ADElectronics/1986BE4-Dev-Board/Firmware/MDR1986BE4_StdPeriph_Driver/src/MDR32F9Qx_dma.c

/**
  * FILE MDR32F9Qx_dma.c
  */

/* Includes ------------------------------------------------------------------*/
#include "MDR32F9Qx_config.h"
#include "MDR32F9Qx_dma.h"

#define ASSERT_INFO_FILE_ID FILEID__MDR32F9X_DMA_C

/** @addtogroup __MDR32F9Qx_StdPeriph_Driver MDR32F9Qx Standard Peripherial Driver
  * @{
  */

/** @defgroup DMA DMA
  * @{
  */

/** @defgroup DMA_Private_Constants DMA Private Constants
  * @{
  */

#define DMA_CONTROL_MINUS_1   ((uint32_t)0x3FF0)      /* DMA control "n_minus_1" field mask */

/** @} */ /* End of group DMA_Private_Constants */

/** @defgroup DMA_Private_Variables DMA Private Variables
  * @{
  */

/**
  * @brief  DMA Channel Control Data Table
  */

/* Select data alignment */
#if (DMA_Channels_Number == 1)
#define DATA_ALIGN 32
#elif (DMA_Channels_Number == 2)
#define DATA_ALIGN 64
#elif ((DMA_Channels_Number >= 3) && (DMA_Channels_Number <= 4))
#define DATA_ALIGN 128
#elif ((DMA_Channels_Number >= 5) && (DMA_Channels_Number <= 8))
#define DATA_ALIGN 256
#elif ((DMA_Channels_Number >= 9) && (DMA_Channels_Number <= 16))
#define DATA_ALIGN 512
#elif ((DMA_Channels_Number >= 17) && (DMA_Channels_Number <= 32))
#define DATA_ALIGN 1024
#endif

#if defined ( __ICCARM__ )
  #pragma data_alignment = DATA_ALIGN
	DMA_CtrlDataTypeDef DMA_ControlTable[DMA_Channels_Number * (1 + DMA_AlternateData)];
#endif

#if defined ( __CMCARM__ )
	#pragma locate DMA_ControlTable 0x20000000 noinit
	DMA_CtrlDataTypeDef DMA_ControlTable[DMA_Channels_Number * (1 + DMA_AlternateData)];
#elif defined ( __CC_ARM )
	DMA_CtrlDataTypeDef DMA_ControlTable[DMA_Channels_Number * (1 + DMA_AlternateData)] __attribute__ ((aligned (DATA_ALIGN)));
#elif defined ( __GNUC__ )
	DMA_CtrlDataTypeDef DMA_ControlTable[DMA_Channels_Number * (1 + DMA_AlternateData)] __attribute__((aligned(DATA_ALIGN)));
#endif


/** @} */ /* End of group DMA_Private_Variables */

/** @defgroup DMA_Private_FunctionPrototypes DMA Private Function Prototypes
  * @{
  */

void DMA_CtrlDataInit(DMA_CtrlDataInitTypeDef *DMA_ctrl_data_ptr, DMA_CtrlDataTypeDef *DMA_ctrl_table_ptr);

/** @} */ /* End of group DMA_Private_FunctionPrototypes */

/** @defgroup DMA_Private_Functions DMA Private Functions
  * @{
  */

/**
  * @brief  Initializes the DMA control data structure according to the specified
  *         parameters.
  * @param  DMA_ctrl_data_ptr: pointer to a DMA_CtrlDataInitTypeDef structure that
  *         contains the control data structure to initialize
  * @param  DMA_ctrl_table_ptr: pointer to a DMA_CtrlDataTypeDef structure that
  *         contains the initial control data configuration, provided by the application.
  * @retval None
  */
void DMA_CtrlDataInit(DMA_CtrlDataInitTypeDef *DMA_ctrl_data_ptr, DMA_CtrlDataTypeDef *DMA_ctrl_table_ptr)
{
  /* Check DMA configuration parameters */
  assert_param(IS_DMA_CHANNELS(DMA_Channels_Number));
  assert_param(IS_DMA_ALTERNATE_DATA(DMA_AlternateData));

  /* Check the parameters */
  assert_param(IS_DMA_SOURCE_INC_STATE(DMA_ctrl_data_ptr->DMA_SourceIncSize));
  assert_param(IS_DMA_DEST_INC_STATE(DMA_ctrl_data_ptr->DMA_DestIncSize));
  assert_param(IS_DMA_MEMORY_DATA_SIZE(DMA_ctrl_data_ptr->DMA_MemoryDataSize));
  assert_param(IS_DMA_MODE(DMA_ctrl_data_ptr->DMA_Mode));
  assert_param(IS_DMA_CYCLE_SIZE(DMA_ctrl_data_ptr->DMA_CycleSize));
  assert_param(IS_DMA_CONTINUOUS_NUMBER(DMA_ctrl_data_ptr->DMA_NumContinuous));
  assert_param(IS_DMA_SOURCE_PROT(DMA_ctrl_data_ptr->DMA_SourceProtCtrl));
  assert_param(IS_DMA_DEST_PROT(DMA_ctrl_data_ptr->DMA_DestProtCtrl));

  /* DMA Source Data End Address */
  if (DMA_ctrl_data_ptr->DMA_SourceIncSize == DMA_SourceIncNo)
  {
    DMA_ctrl_table_ptr->DMA_SourceEndAddr = DMA_ctrl_data_ptr->DMA_SourceBaseAddr;
  }
  else
  {
    DMA_ctrl_table_ptr->DMA_SourceEndAddr = ( DMA_ctrl_data_ptr->DMA_SourceBaseAddr +
        ((DMA_ctrl_data_ptr->DMA_CycleSize - 1) << (DMA_ctrl_data_ptr->DMA_SourceIncSize >> 26)));
  }

  /* DMA Destination Data End Address */
  if (DMA_ctrl_data_ptr->DMA_Mode == DMA_Mode_MemScatterPri)
  {
    /* Memory Scatter-Gather mode */
    DMA_ctrl_table_ptr->DMA_DestEndAddr = (DMA_ctrl_data_ptr->DMA_DestBaseAddr + 12);
  }
  else
  {
    /* Other modes */
    if (DMA_ctrl_data_ptr->DMA_DestIncSize == DMA_DestIncNo)
    {
      DMA_ctrl_table_ptr->DMA_DestEndAddr = DMA_ctrl_data_ptr->DMA_DestBaseAddr;
    }
    else
    {
      DMA_ctrl_table_ptr->DMA_DestEndAddr = ( DMA_ctrl_data_ptr->DMA_DestBaseAddr +
        ((DMA_ctrl_data_ptr->DMA_CycleSize - 1) << (DMA_ctrl_data_ptr->DMA_DestIncSize >> 30)));
    }
  }

  /* DMA Control Data */
  DMA_ctrl_table_ptr->DMA_Control = (DMA_ctrl_data_ptr->DMA_DestIncSize     |
                                     DMA_ctrl_data_ptr->DMA_MemoryDataSize  |
                                     DMA_ctrl_data_ptr->DMA_SourceIncSize   |
                                     DMA_ctrl_data_ptr->DMA_DestProtCtrl    |
                                     DMA_ctrl_data_ptr->DMA_SourceProtCtrl  |
                                     DMA_ctrl_data_ptr->DMA_NumContinuous   |
                                     ((DMA_ctrl_data_ptr->DMA_CycleSize - 1) << 4)  |
                                     DMA_ctrl_data_ptr->DMA_Mode);
}

/**
  * @brief  Deinitializes the DMA registers to their default reset values.
  * @param  None
  * @retval None
  */
void DMA_DeInit(void)
{
  MDR_DMA->CFG = 0;                           /* Master Enable Off */
  MDR_DMA->CTRL_BASE_PTR = 0;                 /* Control data base pointer */
  MDR_DMA->CHNL_SW_REQUEST = 0;               /* Disable all sw requests */
  MDR_DMA->CHNL_USEBURST_CLR = 0xFFFFFFFF;    /* Disable burst mode */
  MDR_DMA->CHNL_REQ_MASK_CLR = 0xFFFFFFFF;    /* Clear mask request */
  MDR_DMA->CHNL_ENABLE_CLR = 0xFFFFFFFF;      /* Clear channel enable */
  MDR_DMA->CHNL_PRI_ALT_CLR = 0xFFFFFFFF;     /* Reset to primary data structure */
  MDR_DMA->CHNL_PRIORITY_CLR = 0xFFFFFFFF;    /* Reset to default priority */
  MDR_DMA->ERR_CLR = 0x01;                    /* Clear dma_err status */
}

/**
  * @brief  Initializes the DMA Channel DMA_ControlTable structure according to the specified
  *         parameters.
  * @param  DMA_Channel: can be 0 to 31 or a value of @ref DMA_valid_channels to select the DMA Channel.
  * @param  DMA_CtrlDataType: can be DMA_CTRL_DATA_PRIMARY or DMA_CTRL_DATA_ALTERNATE
  * @param  DMA_CtrlStruct: pointer to a DMA_CtrlDataInitTypeDef structure that
  *         contains the initial control data configuration, provided by the application
  * 				for the specified DMA Channel.
  * @retval None
  */
void DMA_CtrlInit(uint8_t DMA_Channel, uint8_t DMA_CtrlDataType,  DMA_CtrlDataInitTypeDef* DMA_CtrlStruct)
{
  /* Primary Control Data Init */
  if (DMA_CtrlDataType == DMA_CTRL_DATA_PRIMARY)
  {
    DMA_CtrlDataInit(DMA_CtrlStruct, &DMA_ControlTable[DMA_Channel]);
  }
#if (DMA_AlternateData == 1)
  /* Alternate Control Data Init */
  else
  {
    uint32_t ptr = (MDR_DMA->ALT_CTRL_BASE_PTR + (DMA_Channel * sizeof(DMA_CtrlDataTypeDef)));
    DMA_CtrlDataInit(DMA_CtrlStruct, (DMA_CtrlDataTypeDef *)ptr);
  }
#endif
}

/**
  * @brief  Initializes the DMA Scatter-Gather Task structure according to the specified
  *         parameters.
  * @param  DMA_Task: specifies the current task number. Begins with 0.
  * @param  DMA_CtrlStruct: pointer to a DMA_CtrlDataInitTypeDef structure that
  *         contains the control data information for the specified task.
  * @param  DMA_SG_TaskArray: pointer to a DMA_CtrlDataTypeDef array that
  *         contains the copy of the alternate control data information for the specified task.
  * @retval None
  */
void DMA_SG_CtrlInit(uint32_t DMA_Task, DMA_CtrlDataTypeDef *DMA_SG_TaskArray,  DMA_CtrlDataInitTypeDef* DMA_CtrlStruct)
{
  DMA_CtrlDataInit(DMA_CtrlStruct, &DMA_SG_TaskArray[DMA_Task]);
}

/**
  * @brief  Initializes the DMA Channel in Memory Scatter-Gather mode
  * @param  DMA_Channel: can be 0 to 31 or a value of @ref DMA_valid_channels to select the DMA Channel.
  * @param  DMA_SG_InitStruct: pointer to a DMA_Channel_SG_InitTypeDef array that
  *         contains the configuration information for the specified DMA Channel.
  * @retval None
  */
void DMA_SG_Init( uint8_t DMA_Channel, DMA_Channel_SG_InitTypeDef *DMA_SG_InitStruct)
{
  DMA_CtrlDataInitTypeDef DMA_PriCtrlData;

  /* Check the parameters */
  assert_param(DMA_AlternateData == 1);
  assert_param(DMA_SG_InitStruct != 0);
  assert_param(DMA_SG_InitStruct->DMA_SG_TaskNumber != 0);
  assert_param(IS_DMA_CHANNEL(DMA_Channel));
  assert_param(IS_DMA_AHB_PROT(DMA_SG_InitStruct->DMA_ProtCtrl));
  assert_param(IS_DMA_PRIORITY(DMA_SG_InitStruct->DMA_Priority));
  assert_param(IS_DMA_SOURCE_PROT(DMA_SG_InitStruct->DMA_SourceProtCtrl));
  assert_param(IS_DMA_DEST_PROT(DMA_SG_InitStruct->DMA_DestProtCtrl));
  assert_param(IS_DMA_BURST(DMA_SG_InitStruct->DMA_UseBurst));

  /* Check the CTRL_BASE_PTR initialisation */
  MDR_DMA->CTRL_BASE_PTR = (uint32_t)DMA_ControlTable;

  /* Primary Control Data Init */
  DMA_PriCtrlData.DMA_SourceBaseAddr = (uint32_t)(DMA_SG_InitStruct->DMA_SG_TaskArray);
  DMA_PriCtrlData.DMA_DestBaseAddr = (MDR_DMA->ALT_CTRL_BASE_PTR + (DMA_Channel * sizeof(DMA_CtrlDataTypeDef)));
  DMA_PriCtrlData.DMA_SourceIncSize = DMA_SourceIncWord;
  DMA_PriCtrlData.DMA_DestIncSize = DMA_DestIncWord;
  DMA_PriCtrlData.DMA_MemoryDataSize = DMA_MemoryDataSize_Word;
  DMA_PriCtrlData.DMA_Mode = DMA_Mode_MemScatterPri;
  DMA_PriCtrlData.DMA_CycleSize = DMA_SG_InitStruct->DMA_SG_TaskNumber << 2;
  DMA_PriCtrlData.DMA_NumContinuous = DMA_Transfers_4;
  DMA_PriCtrlData.DMA_SourceProtCtrl = DMA_SG_InitStruct->DMA_SourceProtCtrl;
  DMA_PriCtrlData.DMA_DestProtCtrl = DMA_SG_InitStruct->DMA_DestProtCtrl;

  DMA_CtrlDataInit(&DMA_PriCtrlData, &DMA_ControlTable[DMA_Channel]);

  /* DMA configuration register */
  MDR_DMA->CFG = DMA_CFG_MASTER_ENABLE | DMA_SG_InitStruct->DMA_ProtCtrl;

  /* Burst mode */
  if (DMA_SG_InitStruct->DMA_UseBurst == DMA_BurstSet)
  {
    MDR_DMA->CHNL_USEBURST_SET = (1 << DMA_Channel);
  }
  else
  {
    MDR_DMA->CHNL_USEBURST_CLR = (1 << DMA_Channel);
  }

  /* Channel mask clear */
  MDR_DMA->CHNL_REQ_MASK_CLR = (1 << DMA_Channel);

  /* Enable channel */
  MDR_DMA->CHNL_ENABLE_SET = (1 << DMA_Channel);

  /* Primary - Alternate control data structure selection */
  MDR_DMA->CHNL_PRI_ALT_CLR = (1 << DMA_Channel);       /* Use Primary */

  /* Channel priority set */
  if (DMA_SG_InitStruct->DMA_Priority == DMA_Priority_High)
  {
    MDR_DMA->CHNL_PRIORITY_SET = (1 << DMA_Channel);      /* High priority */
  }
  else
  {
    MDR_DMA->CHNL_PRIORITY_CLR = (1 << DMA_Channel);      /* Default priority */
  }
}

/**
  * @brief  Initializes the DMA Channel according to the specified
  *         parameters in the DMA_InitStruct.
  * @param  DMA_Channel: can be 0 to 31 or a value of @ref DMA_valid_channels to select the DMA Channel.
  * @param  DMA_InitStruct: pointer to a DMA_ChannelInitTypeDef structure that
  *         contains the configuration information for the specified DMA Channel.
  * @retval None
  */
void DMA_Init(uint8_t DMA_Channel, DMA_ChannelInitTypeDef* DMA_InitStruct)
{
  /* Check the parameters */
  assert_param(IS_DMA_CHANNEL(DMA_Channel));
  assert_param(IS_DMA_AHB_PROT(DMA_InitStruct->DMA_ProtCtrl));
  assert_param(IS_DMA_PRIORITY(DMA_InitStruct->DMA_Priority));
  assert_param(IS_DMA_BURST(DMA_InitStruct->DMA_UseBurst));
  assert_param(IS_DMA_SELECT_DATA_STRUCTURE(DMA_InitStruct->DMA_SelectDataStructure));

  /* Check the CTRL_BASE_PTR initialisation */
  MDR_DMA->CTRL_BASE_PTR = (uint32_t)DMA_ControlTable;

  /* Primary Control Data Init */
  if (DMA_InitStruct->DMA_PriCtrlData)
  {
    DMA_CtrlDataInit(DMA_InitStruct->DMA_PriCtrlData, &DMA_ControlTable[DMA_Channel]);
  }

#if (DMA_AlternateData == 1)
  /* Alternate Control Data Init */
  if (DMA_InitStruct->DMA_AltCtrlData)
  {
    uint32_t ptr = (MDR_DMA->ALT_CTRL_BASE_PTR + (DMA_Channel * sizeof(DMA_CtrlDataTypeDef)));
    DMA_CtrlDataInit(DMA_InitStruct->DMA_AltCtrlData, (DMA_CtrlDataTypeDef *)ptr);
  }
#endif

  /* DMA configuration register */
  MDR_DMA->CFG = DMA_CFG_MASTER_ENABLE | DMA_InitStruct->DMA_ProtCtrl;

  /* Burst mode */
  if (DMA_InitStruct->DMA_UseBurst == DMA_BurstSet)
  {
    MDR_DMA->CHNL_USEBURST_SET = (1 << DMA_Channel);
  }
  else
  {
    MDR_DMA->CHNL_USEBURST_CLR = (1 << DMA_Channel);
  }

  /* Channel mask clear */
  MDR_DMA->CHNL_REQ_MASK_CLR = (1 << DMA_Channel);

  /* Enable channel */
  MDR_DMA->CHNL_ENABLE_SET = (1 << DMA_Channel);

  /* Primary - Alternate control data structure selection */
  if (DMA_InitStruct->DMA_SelectDataStructure == DMA_CTRL_DATA_PRIMARY)
  {
    MDR_DMA->CHNL_PRI_ALT_CLR = (1 << DMA_Channel);       /* Use Primary */
  }
  else
  {
    MDR_DMA->CHNL_PRI_ALT_SET = (1 << DMA_Channel);       /* Use Alternate */
  }

  /* Channel priority set */
  if (DMA_InitStruct->DMA_Priority == DMA_Priority_High)
  {
    MDR_DMA->CHNL_PRIORITY_SET = (1 << DMA_Channel);      /* High priority */
  }
  else
  {
    MDR_DMA->CHNL_PRIORITY_CLR = (1 << DMA_Channel);      /* Default priority */
  }
}

/**
  * @brief  Fills each DMA_InitStruct member with its default value.
  * @param  DMA_InitStruct : pointer to a DMA_ChannelInitTypeDef structure which will
  *         be initialized.
  * @retval None
  */
void DMA_StructInit(DMA_ChannelInitTypeDef* DMA_InitStruct)
{
  DMA_InitStruct->DMA_PriCtrlData = 0;
  DMA_InitStruct->DMA_AltCtrlData = 0;
  DMA_InitStruct->DMA_ProtCtrl = 0;
  DMA_InitStruct->DMA_Priority = 0;
  DMA_InitStruct->DMA_UseBurst = 0;
  DMA_InitStruct->DMA_SelectDataStructure = 0;
}

/**
  * @brief  Fills each DMA_SG_InitStruct member with its default value.
  * @param  DMA_SG_InitStruct : pointer to a DMA_Channel_SG_InitTypeDef structure which will
  *         be initialized.
  * @retval None
  */
void DMA_SG_StructInit(DMA_Channel_SG_InitTypeDef* DMA_SG_InitStruct)
{
  DMA_SG_InitStruct->DMA_SG_TaskArray = 0;
  DMA_SG_InitStruct->DMA_SG_TaskNumber = 0;
  DMA_SG_InitStruct->DMA_SourceProtCtrl = 0;
  DMA_SG_InitStruct->DMA_DestProtCtrl = 0;
  DMA_SG_InitStruct->DMA_ProtCtrl = 0;
  DMA_SG_InitStruct->DMA_Priority = 0;
  DMA_SG_InitStruct->DMA_UseBurst = 0;
}

/**
  * @brief  Enables or disables the specified DMA Channel.
  * @param  DMA_Channel: can be 0 to 31 or a value of @ref DMA_valid_channels to select the DMA Channel.
  * @param  NewState: new state of the DMA Channel.
  *         This parameter can be: ENABLE or DISABLE.
  * @retval None
  */
void DMA_Cmd(uint8_t DMA_Channel, FunctionalState NewState)
{
  /* Check the parameters */
  assert_param(IS_DMA_CHANNEL(DMA_Channel));

  /* Channel Enable/Disable */
  if ( NewState == ENABLE)
  {
    MDR_DMA->CHNL_ENABLE_SET = (1 << DMA_Channel);
  }
  else
  {
    MDR_DMA->CHNL_ENABLE_CLR = (1 << DMA_Channel);
  }
}

/**
  * @brief  Generates the specified DMA Channel software request.
  * @param  DMA_Channel: can be 0 to 31 or a value of @ref DMA_valid_channels to select the DMA Channel.
  * @retval None
  */
void DMA_Request(uint8_t DMA_Channel)
{
  /* Check the parameters */
  assert_param(IS_DMA_CHANNEL(DMA_Channel));

  /* Set SW Request */
  MDR_DMA->CHNL_SW_REQUEST = (1 << DMA_Channel);
}

/**
  * @brief  Clears the DMA Error bit.
  * @param  None
  * @retval None
  */
void DMA_ClearError(void)
{
  MDR_DMA->ERR_CLR = 0x01;            /* Clear dma_err status */
}

/**
  * @brief  Returns the number of remaining transfers in the current
  *         DMA Channel cycle.
  * @param  DMA_Channel: can be 0 to 31 or a value of @ref DMA_valid_channels to select the DMA Channel.
  * @param  DMA_CtrlData: specifies the primary / alternate control data table to check.
  *         This parameter can be a value of @ref DMA_data_structure_selection.
  * @retval The number of remaining transfers in the current DMA Channel
  *         cycle and the current control data structure.
  */
uint32_t DMA_GetCurrTransferCounter(uint8_t DMA_Channel, uint8_t DMA_CtrlData)
{
  DMA_CtrlDataTypeDef *ptr;     /* Pointer to the channels's data structure */

  /* Check the parameters */
  assert_param(IS_DMA_CHANNEL(DMA_Channel));
  assert_param(IS_DMA_SELECT_DATA_STRUCTURE(DMA_CtrlData));

  /* Init the control data pointer */
  if (DMA_CtrlData == DMA_CTRL_DATA_PRIMARY)
  {
    ptr = (DMA_CtrlDataTypeDef *)(MDR_DMA->CTRL_BASE_PTR + (DMA_Channel * sizeof(DMA_CtrlDataTypeDef)));
  }
  else
  {
    ptr = (DMA_CtrlDataTypeDef *)(MDR_DMA->ALT_CTRL_BASE_PTR + (DMA_Channel * sizeof(DMA_CtrlDataTypeDef)));
  }

  /* Read the number of remaining transfers */
  return (((ptr->DMA_Control & DMA_CONTROL_MINUS_1)>>4) + 1);
}

/**
  * @brief  Checks whether the specified DMA Channel flag is set or not.
  * @param  DMA_Channel: can be 0 to 31 or a value of @ref DMA_valid_channels to select the DMA Channel.
  * @param  DMA_Flag: specifies the flag to check.
  *         This parameter can be one of the following values:
  *           @arg DMA_FLAG_DMA_ENA:       DMA unit global enable status.
  *           @arg DMA_FLAG_DMA_ERR:       DMA unit bus error status.
  *           @arg DMA_FLAG_CHNL_ENA:      DMA channel enable status.
  *           @arg DMA_FLAG_CHNL_MASK:     DMA channel request mask status.
  *           @arg DMA_FLAG_CHNL_WAIT:     DMA channel wait on request status.
  *           @arg DMA_FLAG_CHNL_BURST:    DMA channel burst mode status.
  *           @arg DMA_FLAG_CHNL_ALT:      DMA channel alternate control data status.
  *           @arg DMA_FLAG_CHNL_PRIORITY: DMA channel priority status.
  * @retval The new state of DMA_FLAG (SET or RESET).
  */
FlagStatus DMA_GetFlagStatus(uint8_t DMA_Channel, uint8_t DMA_Flag)
{
  /* Check the parameters */
  assert_param(IS_DMA_CHANNEL(DMA_Channel));
  assert_param(IS_DMA_FLAG(DMA_Flag));

  /* Read Flag Status */
  switch(DMA_Flag)
  {
    case DMA_FLAG_DMA_ENA:
      return (FlagStatus)(MDR_DMA->STATUS & DMA_STATUS_MASTER_ENABLE);
    case DMA_FLAG_DMA_ERR:
      return (FlagStatus)(MDR_DMA->ERR_CLR & 0x01);
    case DMA_FLAG_CHNL_ENA:
      return (FlagStatus)(MDR_DMA->CHNL_ENABLE_SET & (1 << DMA_Channel));
    case DMA_FLAG_CHNL_MASK:
      return (FlagStatus)(MDR_DMA->CHNL_REQ_MASK_SET & (1 << DMA_Channel));
    case DMA_FLAG_CHNL_WAIT:
      return (FlagStatus)(MDR_DMA->WAITONREQ_STATUS & (1 << DMA_Channel));
    case DMA_FLAG_CHNL_BURST:
      return (FlagStatus)(MDR_DMA->CHNL_USEBURST_SET & (1 << DMA_Channel));
    case DMA_FLAG_CHNL_ALT:
      return (FlagStatus)(MDR_DMA->CHNL_PRI_ALT_SET & (1 << DMA_Channel));
    case DMA_FLAG_CHNL_PRIORITY:
      return (FlagStatus)(MDR_DMA->CHNL_PRIORITY_SET & (1 << DMA_Channel));
    default:
      return (FlagStatus)0;
  }
}

/** @} */ /* End of group DMA_Private_Functions */

/** @} */ /* End of group DMA */

/** @} */ /* End of group __MDR32F9Qx_StdPeriph_Driver */

/*
*
* END OF FILE MDR32F9Qx_dma.c */
