ADElectronics/1986BE4-Dev-Board/Firmware/Project/image.h

#ifndef __IMAGE_H__
#define __IMAGE_H__

#include "MDR32F9Qx_config.h"

static const uint16_t img[] =
{
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
};

#endif // __IMAGE_H__
