ADElectronics/1986BE4-Dev-Board/Firmware/Project/lcd_fonts.h

#include <stdint.h>

#ifndef __LCD_FONTS_H__
#define __LCD_FONTS_H__

typedef struct {
	const uint8_t FontWidth;    /*!< Font width in pixels */
	uint8_t FontHeight;   /*!< Font height in pixels */
	const uint16_t *data; /*!< Pointer to data font data array */
} FontDef;


extern FontDef Font_7x10;
extern FontDef Font_11x18;
extern FontDef Font_16x26;

#endif // __LCD_FONTS_H__
