ADElectronics/1986BE4-Dev-Board/Firmware/Project/lcd_ssd1306_tests.c

#include "lcd_ssd1306.h"
#include "lcd_ssd1306_tests.h"
#include <string.h>

void ssd1306_TestBorder() {
    ssd1306_Fill(Black);
   
	uint32_t start = 0;// HAL_GetTick();
    uint32_t end = start;
    uint8_t x = 0;
    uint8_t y = 0;
    do {
        ssd1306_DrawPixel(x, y, Black);

        if((y == 0) && (x < 127))
            x++;
        else if((x == 127) && (y < 63))
            y++;
        else if((y == 63) && (x > 0)) 
            x--;
        else
            y--;

        ssd1306_DrawPixel(x, y, White);
        ssd1306_UpdateScreen();
    
        //HAL_Delay(1);
		end +=100;// = HAL_GetTick();
    } while((end - start) < 8000);
   
    HAL_Delay(1000);
}

void ssd1306_TestFonts() {
    ssd1306_Fill(Black);
    ssd1306_SetCursor(2, 0);
	ssd1306_WriteString("Font 11x18", Font_11x18, White); 
    ssd1306_SetCursor(2, 18);
	ssd1306_WriteString("Font 16x26", Font_16x26, White);
    ssd1306_SetCursor(2, 26+18);
    ssd1306_WriteString("Font 7x10", Font_7x10, White);
    ssd1306_UpdateScreen();
	HAL_Delay(4000);
}

void ssd1306_TestFPS() {
    ssd1306_Fill(White);
   
    uint32_t start = HAL_GetTick();
    uint32_t end = start;
    int fps = 0;
    char message[] = "ABCDEFGHIJK";
   
    ssd1306_SetCursor(2,0);
    ssd1306_WriteString("Testing...", Font_11x18, Black);
   
    do {
        ssd1306_SetCursor(2, 18);
        ssd1306_WriteString(message, Font_11x18, Black);
        ssd1306_UpdateScreen();
       
        char ch = message[0];
        memmove(message, message+1, sizeof(message)-2);
        message[sizeof(message)-2] = ch;

        fps++;
        end = HAL_GetTick();
    } while((end - start) < 5000);
   
    HAL_Delay(1000);

    char buff[64];
    fps = (float)fps / ((end - start) / 1000.0);
    snprintf(buff, sizeof(buff), "~%d FPS", fps);
   
    ssd1306_Fill(White);
    ssd1306_SetCursor(2, 18);
    ssd1306_WriteString(buff, Font_11x18, Black);
    ssd1306_UpdateScreen();
	HAL_Delay(1000);
}

void ssd1306_TestAll() {
    ssd1306_Init();
    ssd1306_TestFPS();
    HAL_Delay(3000);
    ssd1306_TestBorder();
    ssd1306_TestFonts();
}
